smartboxchannel/EFEKTA_eON213z/PROJECT SOURCE/EINK213TH_SIMPLE_TEST/Source/imagedata.c

#include "imagedata.h"
//#include <avr/pgmspace.h>

const unsigned char ZERO[] = { /* 0X01,0X01,0X2C,0X00,0X43,0X00, */
0X00,0X00,0X00,0X00,0X00,0X00,0X00,0X00,0X00,0X00,0X00,0X00,0X00,0X00,0X00,0X00,
0X00,0X00,0X00,0X00,0X00,0X00,0X00,0X00,0X00,0X00,0X00,0X00,0X00,0X00,0X00,0X00,
0X00,0X00,0X00,0X00,0X00,0X0F,0XFF,0XFF,0XFF,0XFF,0XFE,0X00,0X00,0X00,0X3F,0XFF,
0XFF,0XFF,0XFF,0XFF,0XC0,0X00,0X00,0XFF,0XFF,0XFF,0XFF,0XFF,0XFF,0XE0,0X00,0X03,
0XFF,0XFF,0XFF,0XFF,0XFF,0XFF,0XF8,0X00,0X07,0XFF,0XFF,0XFF,0XFF,0XFF,0XFF,0XFC,
0X00,0X0F,0XFF,0XFF,0XFF,0XFF,0XFF,0XFF,0XFC,0X00,0X1F,0XFF,0XFF,0XFF,0XFF,0XFF,
0XFF,0XFE,0X00,0X3F,0XFF,0XFF,0XFF,0XFF,0XFF,0XFF,0XFF,0X00,0X3F,0XFF,0XFF,0XFF,
0XFF,0XFF,0XFF,0XFF,0X00,0X3F,0XFF,0XFF,0XFF,0XFF,0XFF,0XFF,0XFF,0X80,0X7F,0XFF,
0XFF,0XFF,0XFF,0XFF,0XFF,0XFF,0X80,0X7F,0XFF,0XFF,0XFF,0XFF,0XFF,0XFF,0XFF,0XC0,
0X7F,0XFF,0XFF,0XFF,0XFF,0XFF,0XFF,0XFF,0XC0,0X7F,0XFF,0X00,0X00,0X00,0X00,0X06,
0X7F,0XC0,0X3F,0XFC,0X00,0X00,0X00,0X00,0X03,0XCF,0XE0,0X3F,0XF8,0X00,0X00,0X00,
0X00,0X03,0XF3,0XE0,0X1F,0XF0,0X00,0X00,0X00,0X00,0X03,0XF8,0XE0,0X1F,0XF0,0X00,
0X00,0X00,0X00,0X01,0XFC,0X60,0X8F,0XF0,0X00,0X00,0X00,0X00,0X01,0XFE,0X20,0XC7,
0XF0,0X00,0X00,0X00,0X00,0X01,0XFF,0X20,0XE3,0XF0,0X00,0X00,0X00,0X00,0X03,0XFF,
0X00,0XF9,0XF0,0X00,0X00,0X00,0X00,0X03,0XFF,0X80,0XFE,0X78,0X00,0X00,0X00,0X00,
0X07,0XFF,0X80,0XFF,0XEC,0X00,0X00,0X00,0X00,0X0F,0XFF,0X80,0X7F,0XFF,0XFF,0XFF,
0XFF,0XFF,0XFF,0XFF,0X80,0X7F,0XFF,0XFF,0XFF,0XFF,0XFF,0XFF,0XFF,0X80,0X7F,0XFF,
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

const unsigned char I2[] = { /* 0X01,0X01,0X0F,0X00,0X11,0X00, */
0X00,0X00,0X00,0X00,0X3C,0X00,0X00,0XFE,0X00,0X03,0XBF,0X00,0X0E,0X3F,0X00,0X38,
0X3F,0X80,0XE0,0X7F,0X80,0X80,0X7F,0X80,0XE0,0X7F,0X80,0X38,0XFF,0X80,0X0E,0XFF,
0X00,0X03,0XFF,0X00,0X00,0XFE,0X00,0X00,0X3C,0X00,0X00,0X00,0X00,};
