smartboxchannel/EFEKTA_eON213z/PROJECT SOURCE/EINK213TH_SIMPLE_TEST/Source/imagedata.h

extern const unsigned char LOGO[];
extern const unsigned char ESPEC[];
extern const unsigned char ZERO[];
extern const unsigned char ONE[];
extern const unsigned char TWO[];
extern const unsigned char THREE[];
extern const unsigned char FOUR[];
extern const unsigned char FIVE[];
extern const unsigned char SIX[];
extern const unsigned char SEVEN[];
extern const unsigned char EIGHT[];
extern const unsigned char NINE[];

extern const unsigned char ZERO_S[];
extern const unsigned char ONE_S[];
extern const unsigned char TWO_S[];
extern const unsigned char THREE_S[];
extern const unsigned char FOUR_S[];
extern const unsigned char FIVE_S[];
extern const unsigned char SIX_S[];
extern const unsigned char SEVEN_S[];
extern const unsigned char EIGHT_S[];
extern const unsigned char NINE_S[];

extern const unsigned char CELSIUS[];
extern const unsigned char PERCENT[];
extern const unsigned char POINT[];

extern const unsigned char IMAGE_UP[];
extern const unsigned char IMAGE_DOWN[];

extern const unsigned char bz[];
extern const unsigned char b0[];
extern const unsigned char b13[];
extern const unsigned char b25[];
extern const unsigned char b38[];
extern const unsigned char b50[];
extern const unsigned char b63[];
extern const unsigned char b75[];
extern const unsigned char b87[];
extern const unsigned char b100[];

extern const unsigned char I1[];
extern const unsigned char I2[];

extern const unsigned char IMAGE_ONNETWORK[];
extern const unsigned char IMAGE_OFFNETWORK[];
