smartboxchannel/EFEKTA_eON213z/PROJECT SOURCE/EINK213TH_SIMPLE_TEST/Source/zcl_app.h

#ifndef ZCL_APP_H
#define ZCL_APP_H

#ifdef __cplusplus
extern "C" {
#endif

/*********************************************************************
 * INCLUDES
 */
#include "version.h"
#include "zcl.h"


/*********************************************************************
 * CONSTANTS
 */

// Application Events
#define APP_REPORT_EVT                  0x0001
#define APP_READ_SENSORS_EVT            0x0002

#define APP_REPORT_DELAY ((uint32) 60000) //60 sec

/*********************************************************************
 * MACROS
 */

#define R           ACCESS_CONTROL_READ
#define RR          (R | ACCESS_REPORTABLE)

#define BASIC       ZCL_CLUSTER_ID_GEN_BASIC
#define POWER_CFG   ZCL_CLUSTER_ID_GEN_POWER_CFG
#define TEMP        ZCL_CLUSTER_ID_MS_TEMPERATURE_MEASUREMENT
#define HUMIDITY    ZCL_CLUSTER_ID_MS_RELATIVE_HUMIDITY

#define ZCL_UINT8   ZCL_DATATYPE_UINT8
#define ZCL_UINT16  ZCL_DATATYPE_UINT16
#define ZCL_UINT32  ZCL_DATATYPE_UINT32
#define ZCL_INT16   ZCL_DATATYPE_INT16
#define ZCL_INT8    ZCL_DATATYPE_INT8


/*********************************************************************
 * TYPEDEFS
 */

/*********************************************************************
 * VARIABLES
 */

extern SimpleDescriptionFormat_t zclApp_FirstEP;

extern uint8 zclApp_BatteryVoltage;
extern uint8 zclApp_BatteryPercentageRemainig;
extern uint16 zclApp_BatteryVoltageRawAdc;
extern int16 zclApp_Temperature_Sensor_MeasuredValue;
extern uint16 zclApp_HumiditySensor_MeasuredValue;

// attribute list
extern CONST zclAttrRec_t zclApp_AttrsFirstEP[];
extern CONST uint8 zclApp_AttrsFirstEPCount;

extern const uint8 zclApp_ManufacturerName[];
extern const uint8 zclApp_ModelId[];
extern const uint8 zclApp_PowerSource;

// APP_TODO: Declare application specific attributes here

/*********************************************************************
 * FUNCTIONS
 */

/*
 * Initialization for the task
 */
extern void zclApp_Init(byte task_id);

/*
 *  Event Process for the task
 */
extern UINT16 zclApp_event_loop(byte task_id, UINT16 events);


void user_delay_ms(unsigned int delaytime);

#ifdef __cplusplus
}
#endif

#endif /* ZCL_APP_H */
